kajusK/AAWS/cad/anemometer/body/body_top.fcstd

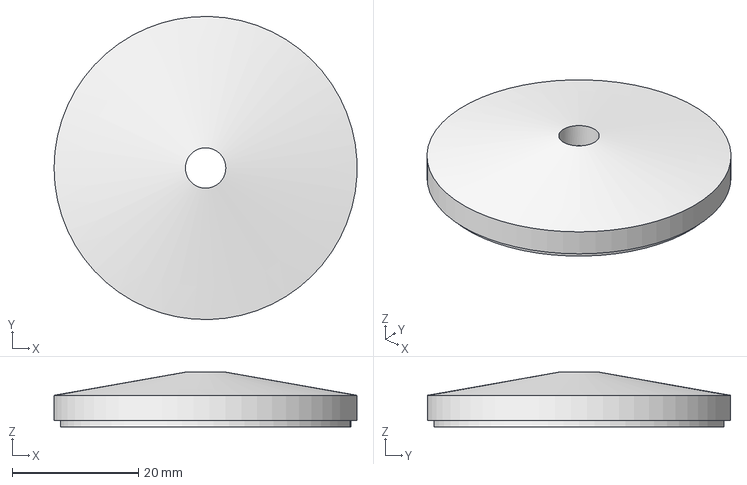
[picture p15: CAD file, 2016-06-13]
cad/anemometer/body/body_top.fcstd
48.0 x 48.0 x 8.67 mm
