kajusK/AAWS/cad/rain_gauge/top.fcstd

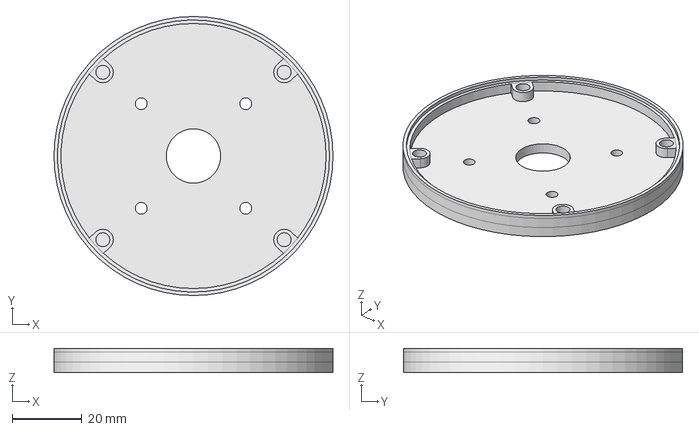
[picture p16: CAD file, 2016-06-22]
cad/rain_gauge/top.fcstd
80.0 x 80.0 x 7.00 mm
