kajusK/AAWS/cad/wind_vane/top/vane.fcstd

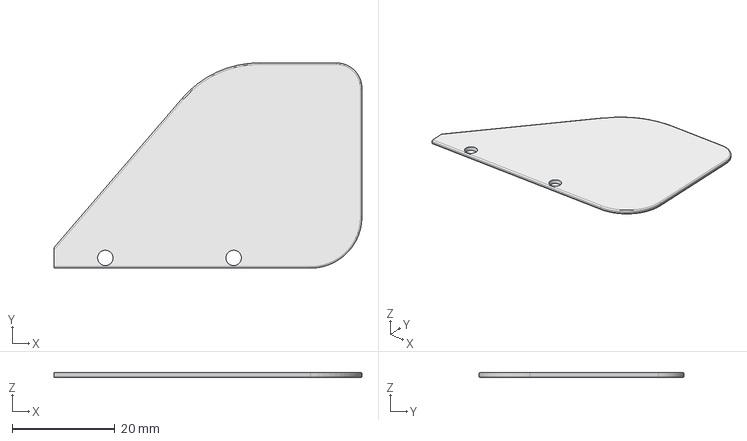
[picture p17: CAD file, 2016-06-03]
cad/wind_vane/top/vane.fcstd
60.0 x 40.0 x 1.00 mm
