kajusK/AAWS/cad/rain_gauge/catcher.fcstd

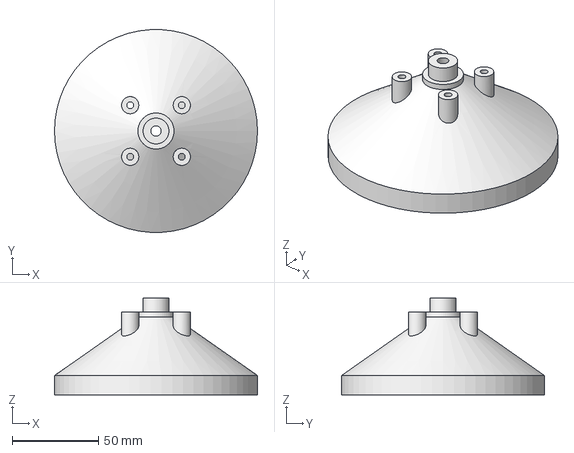
[picture p18: CAD file, 2016-06-22]
cad/rain_gauge/catcher.fcstd
118.0 x 117.8 x 56.3 mm
