kajusK/AAWS/cad/anemometer/body/signal_plate.fcstd

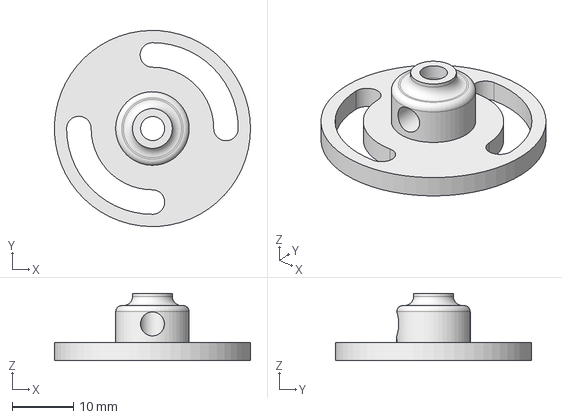
[picture p19: CAD file, 2016-06-13]
cad/anemometer/body/signal_plate.fcstd
32.0 x 32.0 x 11.0 mm
