kajusK/AAWS/cad/rain_gauge/bucket.fcstd

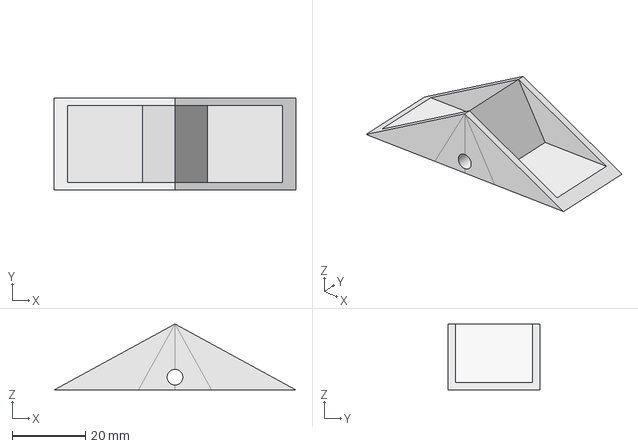
[picture p20: CAD file, 2016-06-22]
cad/rain_gauge/bucket.fcstd
66.0 x 25.0 x 18.0 mm
