kajusK/AAWS/daemon/src/protocol.h

/*
 * Weather station
 *
 * For license, see LICENSE.txt
 *
 * Jakub Kaderka 2016
 */
#ifndef __PROTOCOL_H_
#define __PROTOCOL_H_

struct s_message {
	float temp;
	float humidity;
	float pressure;
	float rain;
	float wind_speed;
	int wind_dir;
};

/*
 * Decode message (#X:123.456;Y:567.89;@) to structure
 */
extern struct s_message decode_message(char *message);

#endif
